MitchellStride/Emergency-Light/Case/Capture.PNG

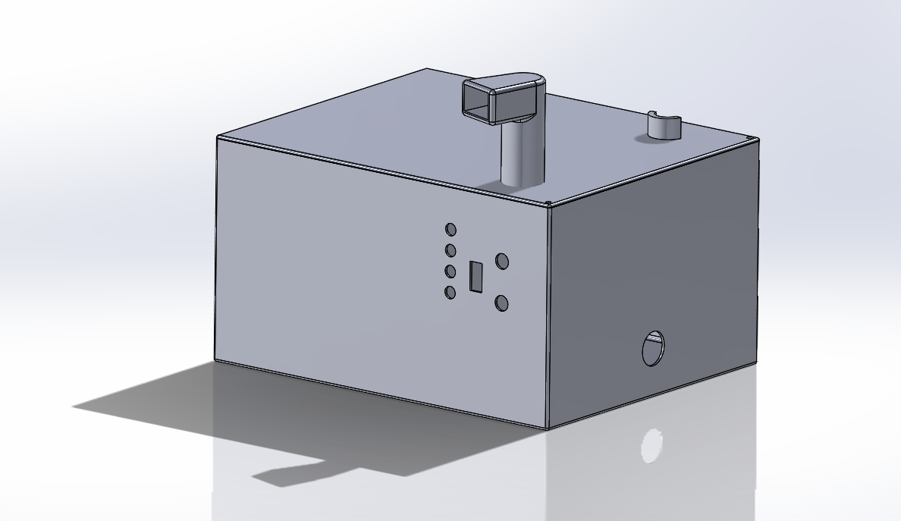
Case/Capture.PNG
