MitchellStride/Emergency-Light/PIC16F684/lab3/CodeCapture.PNG

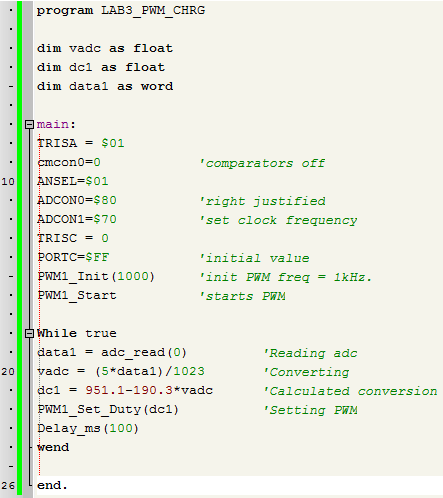
PIC16F684/lab3/CodeCapture.PNG
